qd289942/AI-powered-solutions-for-automated-waste-sorting/ai-training/train-yolov8/Image_processing/background.jpg

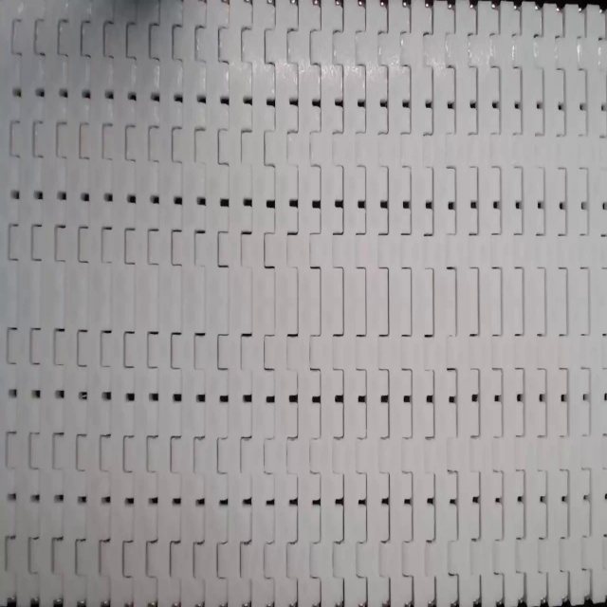
ai-training/train-yolov8/Image_processing/background.jpg
