qd289942/AI-powered-solutions-for-automated-waste-sorting/backend/camera.png

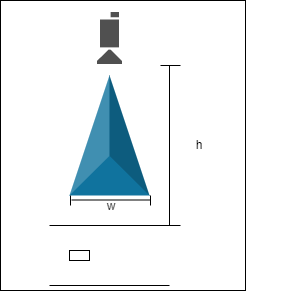
backend/camera.png
