qd289942/AI-powered-solutions-for-automated-waste-sorting/hardware/Camera/Bilder/image.jpg

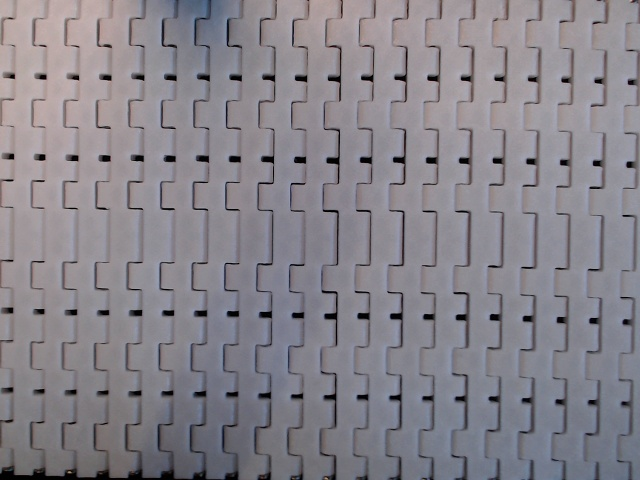
hardware/Camera/Bilder/image.jpg
