qd289942/AI-powered-solutions-for-automated-waste-sorting/hardware/3D Dateien/Front6big.stl

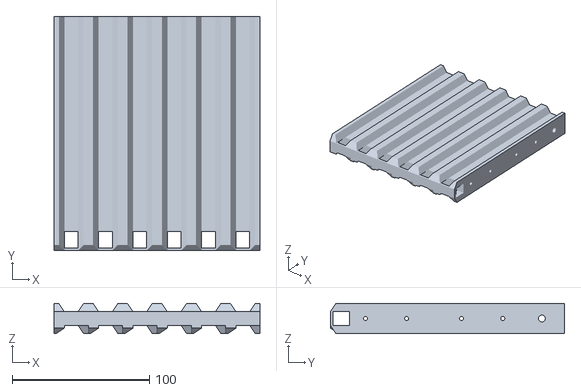
[picture p19: CAD file, 2025-05-03]
hardware/3D Dateien/Front6big.stl
150.0 x 170.5 x 22.0
