qd289942/AI-powered-solutions-for-automated-waste-sorting/hardware/3D Dateien/middle4big.stl

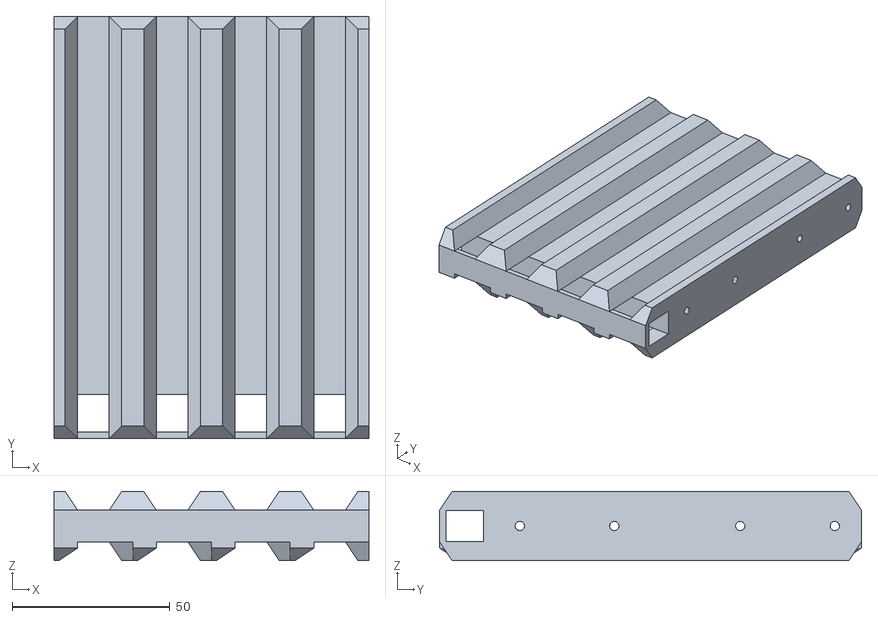
[picture p20: CAD file, 2025-05-03]
hardware/3D Dateien/middle4big.stl
100.0 x 134.0 x 22.0
