qd289942/AI-powered-solutions-for-automated-waste-sorting/hardware/3D Dateien/Fuß.stl

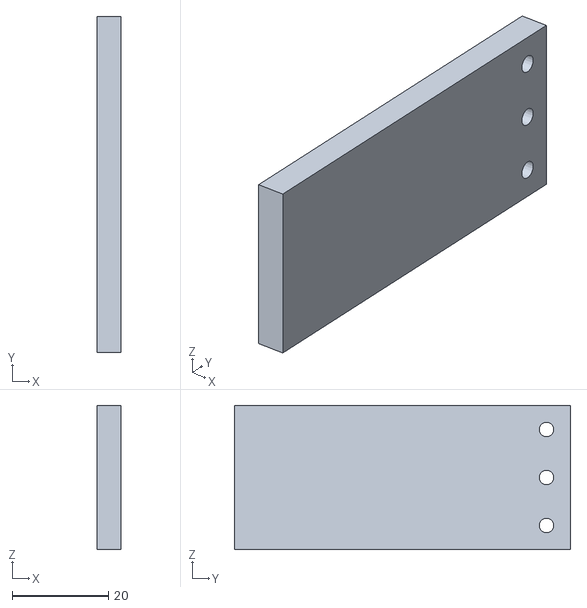
[picture p21: CAD file, 2025-05-03]
hardware/3D Dateien/Fuß.stl
5.00 x 70.0 x 30.0
