qd289942/AI-powered-solutions-for-automated-waste-sorting/hardware/3D Dateien/wheel6big.stl

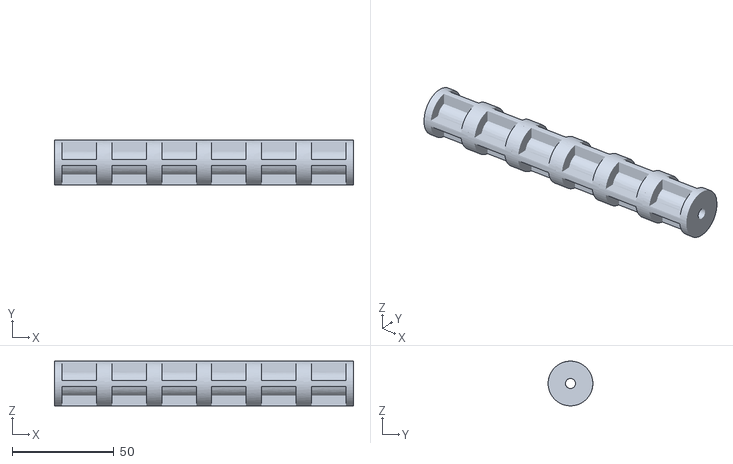
[picture p22: CAD file, 2025-05-03]
hardware/3D Dateien/wheel6big.stl
147.0 x 22.0 x 22.0
