qd289942/AI-powered-solutions-for-automated-waste-sorting/backend/tests/detection/images/woman-640.jpg

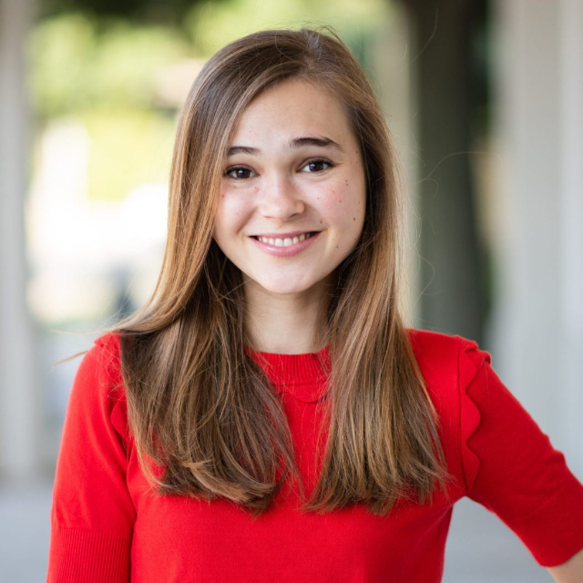
backend/tests/detection/images/woman-640.jpg
