qd289942/AI-powered-solutions-for-automated-waste-sorting/backend/tests/http/tracking/img/640x640/frame_0173.jpg

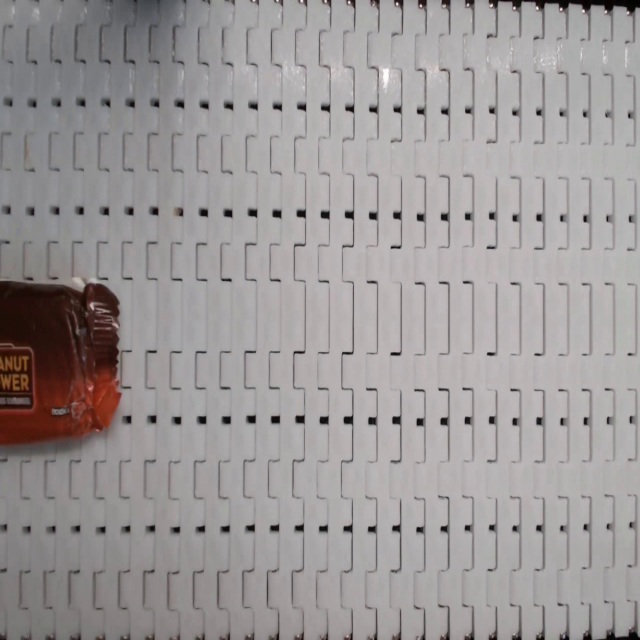
backend/tests/http/tracking/img/640x640/frame_0173.jpg
